Joe2824/Kabeltest/Bilder/2.jpeg

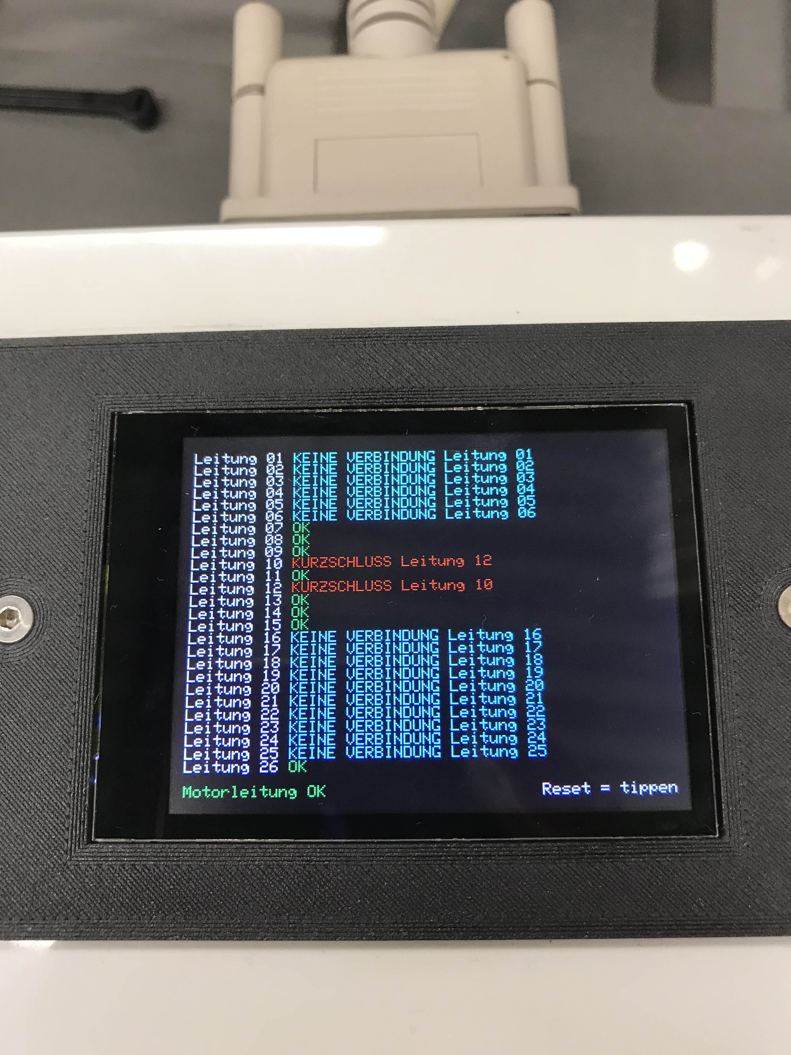
Bilder/2.jpeg
